slugonamission/GaryClock/notes/Calibration.numbers/preview-web.jpg

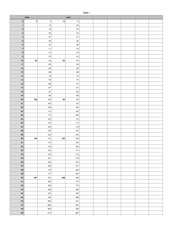
notes/Calibration.numbers/preview-web.jpg
