slugonamission/GaryClock/schematics/power.sch

## EAGLE design schematics/power.sch (2020-05-23)

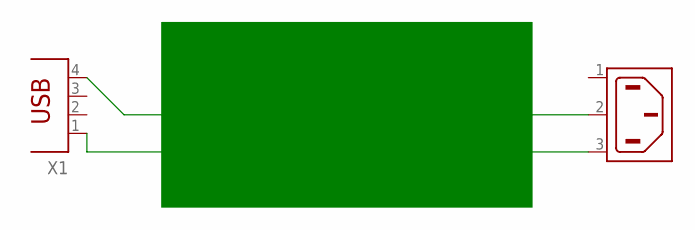
[picture p3: schematic power.sch]

Parts:
X1: PN87520
X2: 6ESRM-P

Connections:
unnamed: X1.4, X2.2 (SH)
unnamed: X1.1, X2.3 (AC2)

Notes on the sheet:
SLUGS TECH CORPORATION
LIMITED CONFIDENTIAL
