slugonamission/GaryClock/src/clock/clock/clock.h

#ifndef __CLOCK_H__
#define __CLOCK_H__


#define RTC_ADDR 0x68

#define PROG_ADDR 0x28

#define SEGL_ADDR 0x70
#define SEGM_ADDR 0x71
#define SEGR_ADDR 0x72

#define BTN_PIN 3

#define RTC_PIN 2
#define RTC_INT 0

#define ARDUINO_LED_PIN 13

#define METER_LEFT_PIN  9
#define METER_MID_PIN   5
#define METER_RIGHT_PIN 10

//#define LEDS_PIN 6 // (actually defined in Leds.h)

#define EEPROM_LEDMODE 0
#define EEPROM_NEUTRINOS 1

#define HOUR 2
#define MINS 1
#define SECS 0

#define NEUTRINOS_PROB 96


#endif
