slugonamission/GaryClock/src/clock/clock/DS1307RTC.cpp

/*
 * DS1307RTC.h - library for DS1307 RTC
  
  Copyright (c) Michael Margolis 2009
  This library is intended to be uses with Arduino Time.h library functions

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
  30 Dec 2009 - Initial release
  5 Sep 2011 updated for Arduino 1.0
 */

#include <Wire.h>
#include "DS1307RTC.h"

#define DS1307_CTRL_ID 0x68 

DS1307RTC::DS1307RTC()
{
  Wire.begin();
}
  
// PUBLIC FUNCTIONS
time_t DS1307RTC::get()   // Aquire data from buffer and convert to time_t
{
  tmElements_t tm;
  if (read(tm) == false) return 0;
  return(makeTime(tm));
}

bool DS1307RTC::set(time_t t)
{
  tmElements_t tm;
  breakTime(t, tm);
  tm.Second |= 0x80;  // stop the clock 
  write(tm); 
  tm.Second &= 0x7f;  // start the clock
  write(tm); 
}

// Aquire data from the RTC chip in BCD format
bool DS1307RTC::read(tmElements_t &tm)
{
  uint8_t sec;
  Wire.beginTransmission(DS1307_CTRL_ID);
#if ARDUINO >= 100  
  Wire.write((uint8_t)0x00); 
#else
  Wire.send(0x00);
#endif  
  if (Wire.endTransmission() != 0) {
    exists = false;
    return false;
  }
  exists = true;

  // request the 7 data fields   (secs, min, hr, dow, date, mth, yr)
  Wire.requestFrom(DS1307_CTRL_ID, tmNbrFields);
  if (Wire.available() < tmNbrFields) return false;
#if ARDUINO >= 100
  sec = Wire.read();
  tm.Second = bcd2dec(sec & 0x7f);   
  tm.Minute = bcd2dec(Wire.read() );
  tm.Hour =   bcd2dec(Wire.read() & 0x3f);  // mask assumes 24hr clock
  tm.Wday = bcd2dec(Wire.read() );
  tm.Day = bcd2dec(Wire.read() );
  tm.Month = bcd2dec(Wire.read() );
  tm.Year = y2kYearToTm((bcd2dec(Wire.read())));
#else
  sec = Wire.receive();
  tm.Second = bcd2dec(sec & 0x7f);   
  tm.Minute = bcd2dec(Wire.receive() );
  tm.Hour =   bcd2dec(Wire.receive() & 0x3f);  // mask assumes 24hr clock
  tm.Wday = bcd2dec(Wire.receive() );
  tm.Day = bcd2dec(Wire.receive() );
  tm.Month = bcd2dec(Wire.receive() );
  tm.Year = y2kYearToTm((bcd2dec(Wire.receive())));
#endif
  if (sec & 0x80) return false; // clock is halted
  return true;
}

bool DS1307RTC::write(tmElements_t &tm)
{
  Wire.beginTransmission(DS1307_CTRL_ID);
#if ARDUINO >= 100  
  Wire.write((uint8_t)0x00); // reset register pointer  
  Wire.write(dec2bcd(tm.Second)) ;   
  Wire.write(dec2bcd(tm.Minute));
  Wire.write(dec2bcd(tm.Hour));      // sets 24 hour format
  Wire.write(dec2bcd(tm.Wday));   
  Wire.write(dec2bcd(tm.Day));
  Wire.write(dec2bcd(tm.Month));
  Wire.write(dec2bcd(tmYearToY2k(tm.Year))); 
#else  
  Wire.send(0x00); // reset register pointer  
  Wire.send(dec2bcd(tm.Second)) ;   
  Wire.send(dec2bcd(tm.Minute));
  Wire.send(dec2bcd(tm.Hour));      // sets 24 hour format
  Wire.send(dec2bcd(tm.Wday));   
  Wire.send(dec2bcd(tm.Day));
  Wire.send(dec2bcd(tm.Month));
  Wire.send(dec2bcd(tmYearToY2k(tm.Year)));   
#endif
  if (Wire.endTransmission() != 0) {
    exists = false;
    return false;
  }
  exists = true;
  return true;
}

// PRIVATE FUNCTIONS

// Convert Decimal to Binary Coded Decimal (BCD)
uint8_t DS1307RTC::dec2bcd(uint8_t num)
{
  return ((num/10 * 16) + (num % 10));
}

// Convert Binary Coded Decimal (BCD) to Decimal
uint8_t DS1307RTC::bcd2dec(uint8_t num)
{
  return ((num/16 * 10) + (num % 16));
}

bool DS1307RTC::setTickMode(bool enabled)
{
  uint8_t tmpReg = 0;
  
  Wire.beginTransmission(DS1307_CTRL_ID);
#if ARDUINO >= 100 
  Wire.write((uint8_t)0x07); // Config ptr
#else
  Wire.send(0x07); // reset register pointer
#endif

  if (Wire.endTransmission() != 0) {
    exists = false;
    return false;
  }
  
  Wire.requestFrom(DS1307_CTRL_ID, 1);
  if (Wire.available() < 1) return false;

#if ARDUINO >= 100
  tmpReg = Wire.read();
#else
  tmpReg = Wire.receive();
#endif

  if(enabled)
    tmpReg |= 0x10;
  else
    tmpReg &= ~0x10;
  
  // Set frequency to 1Hz
  tmpReg &= ~0x03;
    
  Wire.beginTransmission(DS1307_CTRL_ID);
#if ARDUINO >= 100 
  Wire.write((uint8_t)0x07); // Config ptr
  Wire.write(tmpReg);
#else
  Wire.send(0x07); // reset register pointer
  Wire.send(tmpReg);
#endif

  if (Wire.endTransmission() != 0) {
    exists = false;
    return false;
  }

  return true;

}

bool DS1307RTC::exists = false;

DS1307RTC RTC = DS1307RTC(); // create an instance for the user
