slugonamission/GaryClock/src/clock/clock/Voltmeter.h

#ifndef __VOLTMETER_H__
#define __VOLTMETER_H__

#include "Arduino.h"

// Damping parameters
#define USE_DAMPING   1
#define DAMP_DELAY    120
#define DAMP_AMOUNT   69
#define DAMP_DURATION (DAMP_DELAY + DAMP_AMOUNT)

class Voltmeter {
	public:
		Voltmeter(void);
		void begin(int pin);
		void move(uint8_t desiredPosition);
		void moveDamped(uint8_t desiredPosition);
		void moveDamped(uint8_t desiredPosition, uint8_t currentPosition);
		static void moveMultipleDamped(Voltmeter meters[], int count, uint8_t desiredPosition);
		static void moveMultipleDamped(Voltmeter meters[], int count, uint8_t desiredPositions[]);
		uint8_t getPosition(void) { return position; }
	private:
		uint8_t pwmPin;
		uint8_t position;
};

#endif
